dektronics/printalyzer-densitometer/software/desktop/assets/images/media-record.png

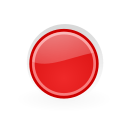
software/desktop/assets/images/media-record.png
