dektronics/printalyzer-densitometer/enclosure/models_2d/stage-plate-rings.dxf

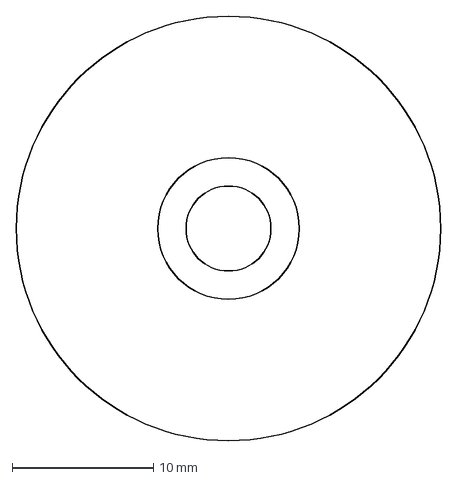
[picture p27: CAD file, 2021-07-16]
enclosure/models_2d/stage-plate-rings.dxf
30.0 x 30.0 mm
