dektronics/printalyzer-densitometer/enclosure/models_3d/jig-upside-down.3mf

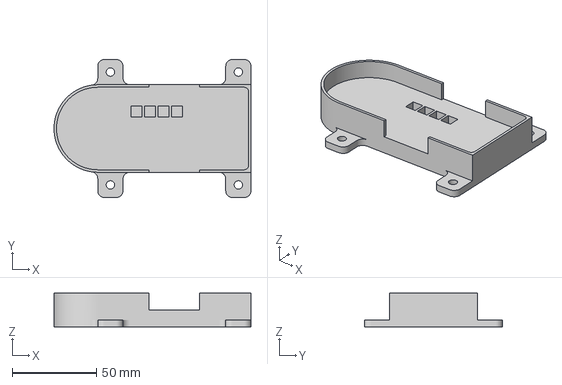
[picture p28: CAD file, 2022-07-06]
enclosure/models_3d/jig-upside-down.3mf
117.0 x 82.0 x 20.0 mm
