dektronics/printalyzer-densitometer/enclosure/models_3d/dens-base-cover.3mf

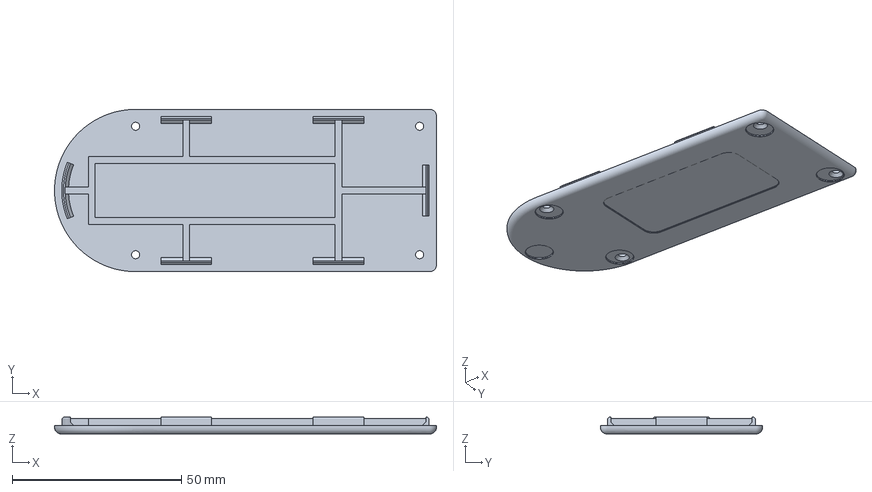
[picture p29: CAD file, 2022-07-06]
enclosure/models_3d/dens-base-cover.3mf
113.0 x 48.0 x 5.00 mm
