dektronics/printalyzer-densitometer/enclosure/models_3d/filter-ring.3mf

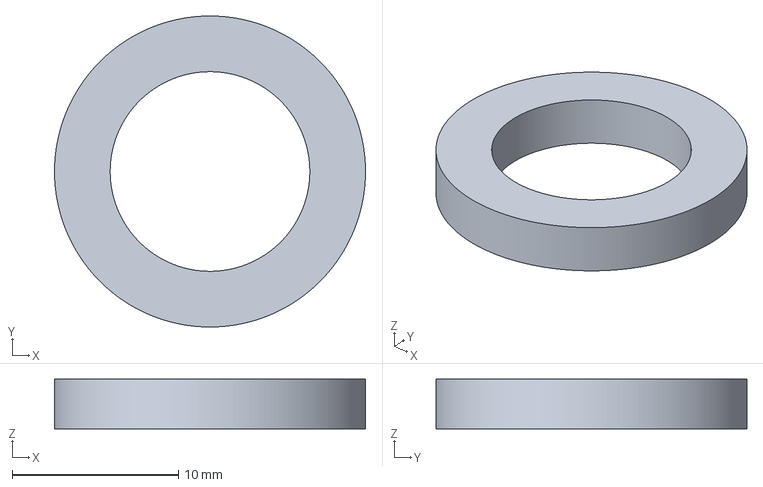
[picture p30: CAD file, 2022-07-06]
enclosure/models_3d/filter-ring.3mf
18.7 x 18.7 x 3.00 mm
