dektronics/printalyzer-densitometer/enclosure/models_3d/dens-base.3mf

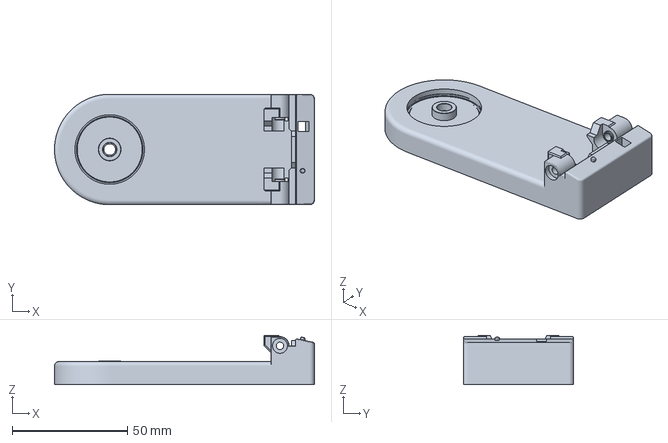
[picture p31: CAD file, 2022-07-06]
enclosure/models_3d/dens-base.3mf
113.0 x 48.0 x 21.3 mm
