dektronics/printalyzer-densitometer/enclosure/models_3d/jig-cal-strip-measure.3mf

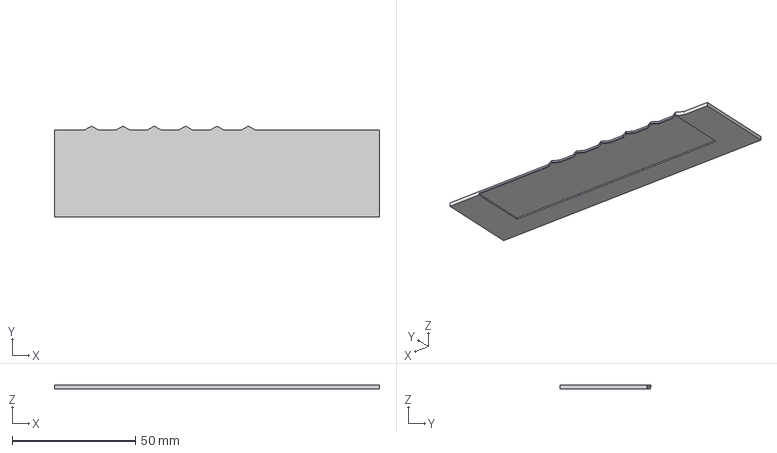
[picture p32: CAD file, 2022-07-06]
enclosure/models_3d/jig-cal-strip-measure.3mf
131.6 x 36.8 x 1.60 mm
