dektronics/printalyzer-densitometer/enclosure/models_3d/jig-spring-trimmer-cover.3mf

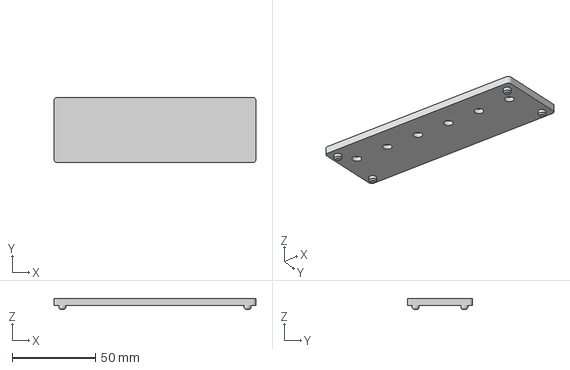
[picture p33: CAD file, 2022-07-06]
enclosure/models_3d/jig-spring-trimmer-cover.3mf
121.0 x 39.2 x 6.50 mm
