dektronics/printalyzer-densitometer/enclosure/models_3d/diffuser-spacer.3mf

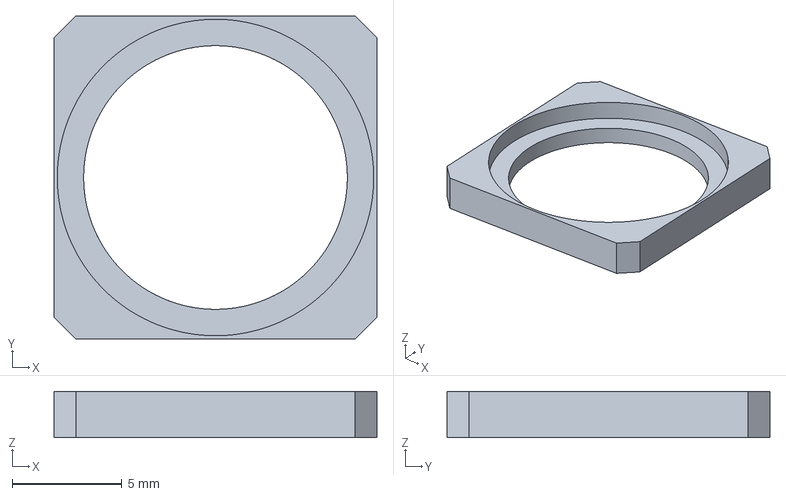
[picture p34: CAD file, 2022-07-06]
enclosure/models_3d/diffuser-spacer.3mf
14.7 x 14.7 x 2.10 mm
