dektronics/printalyzer-densitometer/software/firmware/src/task_main.c

#include "task_main.h"

#include "stm32l0xx_hal.h"
#include <cmsis_os.h>
#include <tusb.h>

#define LOG_TAG "task_main"
#include <elog.h>

#include "cdc_handler.h"
#include "settings.h"
#include "keypad.h"
#include "display.h"
#include "light.h"
#include "task_usbd.h"
#include "task_sensor.h"
#include "adc_handler.h"
#include "state_controller.h"

extern SPI_HandleTypeDef hspi1;
extern TIM_HandleTypeDef htim2;

extern void system_clock_config(void);

static void task_main_run(void *argument);

typedef struct {
    const osThreadFunc_t task_func;
    const osThreadAttr_t task_attrs;
    osThreadId_t task_handle;
} task_params_t;

static osSemaphoreId_t task_start_semaphore = NULL;
static const osSemaphoreAttr_t task_start_semaphore_attributes = {
    .name = "task_start_semaphore"
};

#define TASK_MAIN_STACK_SIZE (2048U)
#define TASK_USBD_STACK_SIZE (1024U)
#define TASK_CDC_STACK_SIZE (1536U)

#ifdef KEYPAD_DEBUG
#define TASK_KEYPAD_STACK_SIZE (768U)
#else
#define TASK_KEYPAD_STACK_SIZE (256U)
#endif

#define TASK_SENSOR_STACK_SIZE (1024U)

static task_params_t task_list[] = {
    {
        .task_func = task_main_run,
        .task_attrs = {
            .name = "main",
            .stack_size = TASK_MAIN_STACK_SIZE,
            .priority = osPriorityNormal
        }
    },
    {
        .task_func = task_usbd_run,
        .task_attrs = {
            .name = "usbd",
            .stack_size = TASK_USBD_STACK_SIZE,
            .priority = osPriorityNormal2 // example uses max-1
        }
    },
    {
        .task_func = task_cdc_run,
        .task_attrs = {
            .name = "cdc",
            .stack_size = TASK_CDC_STACK_SIZE,
            .priority = osPriorityNormal1 // example uses max-2
        }
    },
    {
        .task_func = task_keypad_run,
        .task_attrs = {
            .name = "keypad",
            .stack_size = TASK_KEYPAD_STACK_SIZE,
            .priority = osPriorityNormal
        }
    },
    {
        .task_func = task_sensor_run,
        .task_attrs = {
            .name = "sensor",
            .stack_size = TASK_SENSOR_STACK_SIZE,
            .priority = osPriorityNormal
        }
    }
};

static bool main_task_running = false;

osStatus_t task_main_init()
{
    /* Create the semaphore used to synchronize task startup */
    task_start_semaphore = osSemaphoreNew(1, 0, &task_start_semaphore_attributes);
    if (!task_start_semaphore) {
        log_e("task_start_semaphore create error");
        return osErrorNoMemory;
    }

    /* Create the main task */
    task_list[0].task_handle = osThreadNew(task_list[0].task_func, NULL, &task_list[0].task_attrs);
    if (!task_list[0].task_handle) {
        log_e("main_task create error");
        return osErrorNoMemory;
    }
    return osOK;
}

bool task_main_is_running()
{
    return main_task_running;
}

void task_main_run(void *argument)
{
    const uint8_t task_count = sizeof(task_list) / sizeof(task_params_t);

    log_d("main_task start");

    /* Initialize the display */
    display_init(&hspi1);
    display_clear();

    /* Initialize the light source */
    light_init(&htim2, TIM_CHANNEL_2, TIM_CHANNEL_1);

    /* Load system settings */
    settings_init();

    /* Initialize the ADC handler */
    adc_handler_init();

    /* Initialize the state controller */
    state_controller_init();

    /* Loop through the remaining tasks and create them */
    for (uint8_t i = 1; i < task_count; i++) {
        /* Create the next task */
        task_list[i].task_handle = osThreadNew(task_list[i].task_func, task_start_semaphore, &task_list[i].task_attrs);
        if (!task_list[i].task_handle) {
            log_e("%s create error", task_list[i].task_attrs.name);
            continue;
        }

        /* Wait for the semaphore set once the task initializes */
        if (osSemaphoreAcquire(task_start_semaphore, portMAX_DELAY) != osOK) {
            log_e("Unable to acquire task_start_semaphore");
            return;
        }
    }

    main_task_running = true;

    /* Run the infinite main loop */
    log_i("Starting controller loop");
    state_controller_loop();
}

osStatus_t task_main_force_state(state_identifier_t next_state)
{
    if (next_state >= STATE_MAX) { return osErrorParameter; }

    osStatus_t result = osOK;
    keypad_event_t key_event = {
        .key = KEYPAD_FORCE_TIMEOUT,
        .pressed = true
    };

    do {
        /* Clear any pending keypad events */
        result = keypad_clear_events();
        if (result != osOK) { break; }

        /* Inject a key event to make menu key handlers hit timeouts */
        result = keypad_inject_event(&key_event);

        /* Clear any pending task notifications */
        if (xTaskNotifyStateClear(task_list[0].task_handle) != osOK) {
            result = osError;
            break;
        }

        /* Set the task notification for the state change */
        result = osThreadFlagsSet(task_list[0].task_handle, next_state | 0x40000000);
        if (result != osOK) { break; }
    } while (0);

    return result;
}
