dektronics/printalyzer-densitometer/software/firmware/src/display_assets.c

#include "display_assets.h"

#include <string.h>

#define asset_reflection_40_width 40
#define asset_reflection_40_height 40
static const unsigned char asset_reflection_40_bits[] = {
    0x00, 0x00, 0x3c, 0x00, 0x00, 0x00, 0x00, 0x3c, 0x00, 0x00, 0x00, 0x00,
    0x3c, 0x00, 0x00, 0x00, 0x00, 0x3c, 0x00, 0x00, 0x00, 0x00, 0x3c, 0x00,
    0x00, 0x00, 0xc0, 0xff, 0x03, 0x00, 0x00, 0xf0, 0xff, 0x0f, 0x00, 0x00,
    0xf8, 0xff, 0x1f, 0x00, 0x00, 0xfe, 0x3c, 0x7f, 0x00, 0x00, 0x3f, 0x3c,
    0xfc, 0x00, 0x00, 0x0f, 0x3c, 0xf0, 0x00, 0x80, 0x07, 0x3c, 0xe0, 0x01,
    0xc0, 0x03, 0x00, 0xc0, 0x03, 0xc0, 0x03, 0x00, 0xc0, 0x03, 0xe0, 0x01,
    0x00, 0x80, 0x07, 0xe0, 0x01, 0x00, 0x80, 0x07, 0xe0, 0x00, 0x00, 0x00,
    0x07, 0xe0, 0x00, 0x00, 0x00, 0x07, 0xff, 0x0f, 0x18, 0xf0, 0xff, 0xff,
    0x0f, 0x3c, 0xf0, 0xff, 0xff, 0x0f, 0x3c, 0xf0, 0xff, 0xff, 0x0f, 0x18,
    0xf0, 0xff, 0xe0, 0x00, 0x00, 0x00, 0x07, 0xe0, 0x00, 0x00, 0x00, 0x07,
    0xe0, 0x01, 0x00, 0x80, 0x07, 0xe0, 0x01, 0x00, 0x80, 0x07, 0xc0, 0x03,
    0x00, 0xc0, 0x03, 0xc0, 0x03, 0x00, 0xc0, 0x03, 0x80, 0x07, 0x3c, 0xe0,
    0x01, 0x00, 0x0f, 0x3c, 0xf0, 0x00, 0x00, 0x3f, 0x3c, 0xfc, 0x00, 0x00,
    0xfe, 0x3c, 0x7f, 0x00, 0x00, 0xf8, 0xff, 0x1f, 0x00, 0x00, 0xf0, 0xff,
    0x0f, 0x00, 0x00, 0xc0, 0xff, 0x03, 0x00, 0x00, 0x00, 0x3c, 0x00, 0x00,
    0x00, 0x00, 0x3c, 0x00, 0x00, 0x00, 0x00, 0x3c, 0x00, 0x00, 0x00, 0x00,
    0x3c, 0x00, 0x00, 0x00, 0x00, 0x3c, 0x00, 0x00 };

#define asset_reflection_40_1_width 40
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
    0xfe, 0x00, 0x7f, 0x00, 0x00, 0xf8, 0xff, 0x1f, 0x00, 0x00, 0xf0, 0xff,
    0x0f, 0x00, 0x00, 0xc0, 0xff, 0x03, 0x00, 0x00, 0x00, 0x00, 0x00, 0x00,
    0x00, 0x00, 0x00, 0x00, 0x00, 0x00, 0x00, 0x00, 0x00, 0x00, 0x00, 0x00,
    0x00, 0x00, 0x00, 0x00, 0x00, 0x00, 0x00, 0x00 };

#define asset_zero_indicator_width 14
#define asset_zero_indicator_height 14
static const unsigned char asset_zero_indicator_bits[] = {
    0xe0, 0x01, 0xf8, 0x07, 0x0c, 0x0c, 0x06, 0x18, 0xc2, 0x10, 0xc3, 0x30,
    0xc3, 0x30, 0xf3, 0x33, 0xe3, 0x31, 0xc2, 0x10, 0x06, 0x18, 0x0c, 0x0c,
    0xf8, 0x07, 0xe0, 0x01 };

#define ASSET_ENTRY(x) { x##_bits, x##_width, x##_height }

static const asset_info_t asset_list[] = {
    ASSET_ENTRY(asset_reflection_40),
    ASSET_ENTRY(asset_reflection_40_1),
    ASSET_ENTRY(asset_reflection_40_2),
    ASSET_ENTRY(asset_transmission_40),
    ASSET_ENTRY(asset_transmission_40_1),
    ASSET_ENTRY(asset_transmission_40_2),
    ASSET_ENTRY(asset_zero_indicator)
};

uint8_t display_asset_get(asset_info_t *asset_info, asset_name_t asset_name)
{
    if (asset_info && asset_name >= 0 && asset_name < ASSET_MAX) {
        memcpy(asset_info, &asset_list[asset_name], sizeof(asset_info_t));
        return 1;
    } else {
        return 0;
    }
}
